Robitza777/ESP32-Controller-Personal-Project/hardware/schematics/Controller.kicad_sch

## KiCad design hardware/schematics/Controller.kicad_sch (2026-09-25)

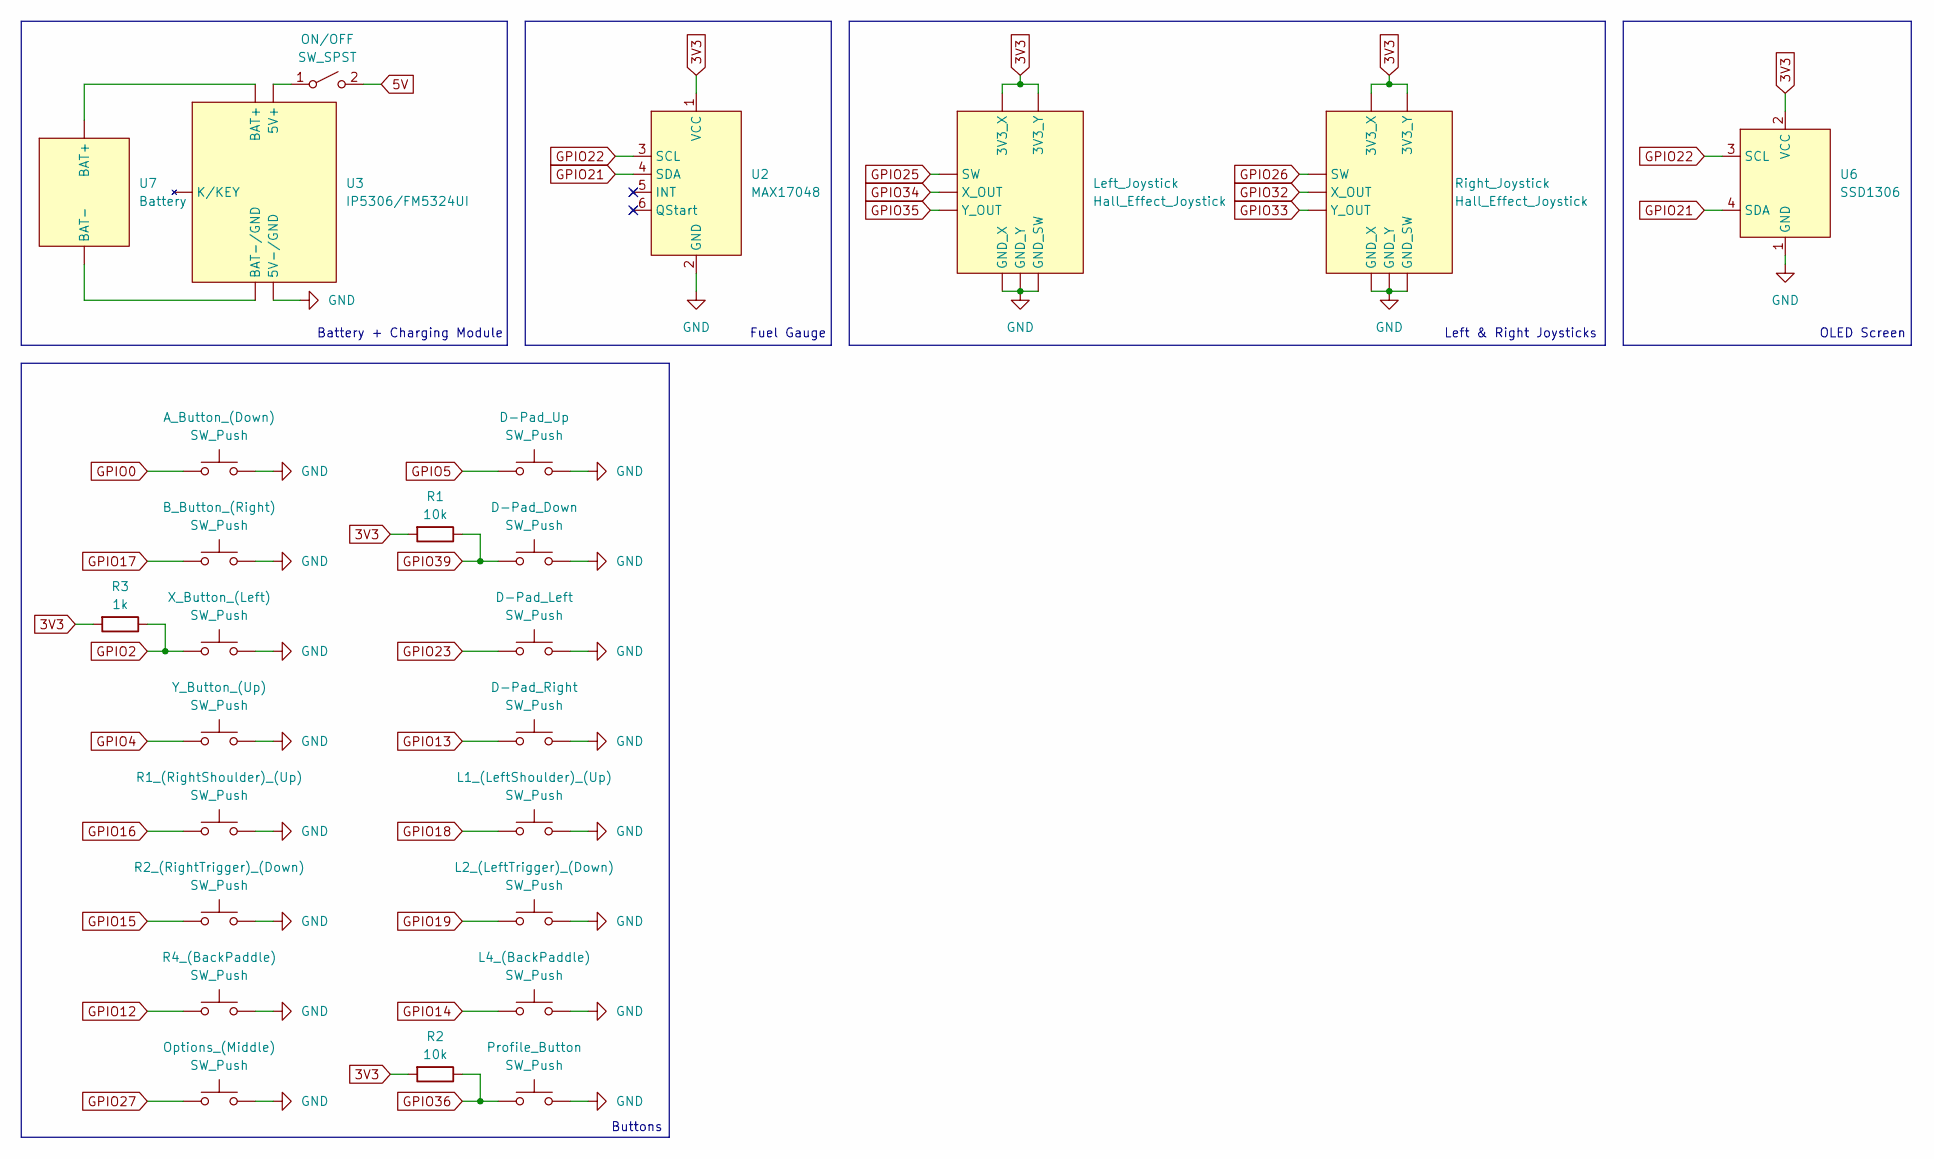
[picture p16: schematic Controller.kicad_sch]

Parts:
A_Button_(Down): SW_Push
B_Button_(Right): SW_Push
D-Pad_Down: SW_Push
D-Pad_Left: SW_Push
D-Pad_Right: SW_Push
D-Pad_Up: SW_Push
L1_(LeftShoulder)_(Up), L2_(LeftTrigger)_(Down), L4_(BackPaddle): SW_Push
Left_Joystick: Hall_Effect_Joystick
ON/OFF: SW_SPST
Options_(Middle): SW_Push
Profile_Button: SW_Push
R1, R2: 10k
R1_(RightShoulder)_(Up), R2_(RightTrigger)_(Down), R4_(BackPaddle): SW_Push
R3: 1k
Right_Joystick: Hall_Effect_Joystick
U2: MAX17048
U3: IP5306/FM5324UI
U6: SSD1306
U7: Battery
X_Button_(Left): SW_Push
Y_Button_(Up): SW_Push

Connections:
3V3: Left_Joystick., R1.2, R2.2, R3.2, Right_Joystick., U2.1 (VCC), U6.2 (VCC)
5V: ON/OFF.2 (B)
GND: A_Button_(Down).2, B_Button_(Right).2, D-Pad_Down.2, D-Pad_Left.2, D-Pad_Right.2, D-Pad_Up.2, L1_(LeftShoulder)_(Up).2, L2_(LeftTrigger)_(Down).2, L4_(BackPaddle).2, Left_Joystick., Options_(Middle).2, Profile_Button.2, R1_(RightShoulder)_(Up).2, R2_(RightTrigger)_(Down).2, R4_(BackPaddle).2, Right_Joystick., U2.2 (GND), U3., U6.1 (GND), X_Button_(Left).2, Y_Button_(Up).2
GPIO0: A_Button_(Down).1
GPIO2: R3.1, X_Button_(Left).1
GPIO4: Y_Button_(Up).1
GPIO5: D-Pad_Up.1
GPIO12: R4_(BackPaddle).1
GPIO13: D-Pad_Right.1
GPIO14: L4_(BackPaddle).1
GPIO15: R2_(RightTrigger)_(Down).1
GPIO16: R1_(RightShoulder)_(Up).1
GPIO17: B_Button_(Right).1
GPIO18: L1_(LeftShoulder)_(Up).1
GPIO19: L2_(LeftTrigger)_(Down).1
GPIO21: U2.4 (SDA), U6.4 (SDA)
GPIO22: U2.3 (SCL), U6.3 (SCL)
GPIO23: D-Pad_Left.1
GPIO25: Left_Joystick.
GPIO26: Right_Joystick.
GPIO27: Options_(Middle).1
GPIO32: Right_Joystick.
GPIO33: Right_Joystick.
GPIO34: Left_Joystick.
GPIO35: Left_Joystick.
GPIO36: Profile_Button.1, R2.1
GPIO39: D-Pad_Down.1, R1.1
unnamed: ON/OFF.1 (A), U3.
unnamed: U3., U7.

Notes on the sheet:
Battery + Charging Module
Fuel Gauge
OLED Screen
Left & Right Joysticks
Buttons
